marian-muenn/eib-drumcomputer/kicad/midi-interface/midi-interface-1.png

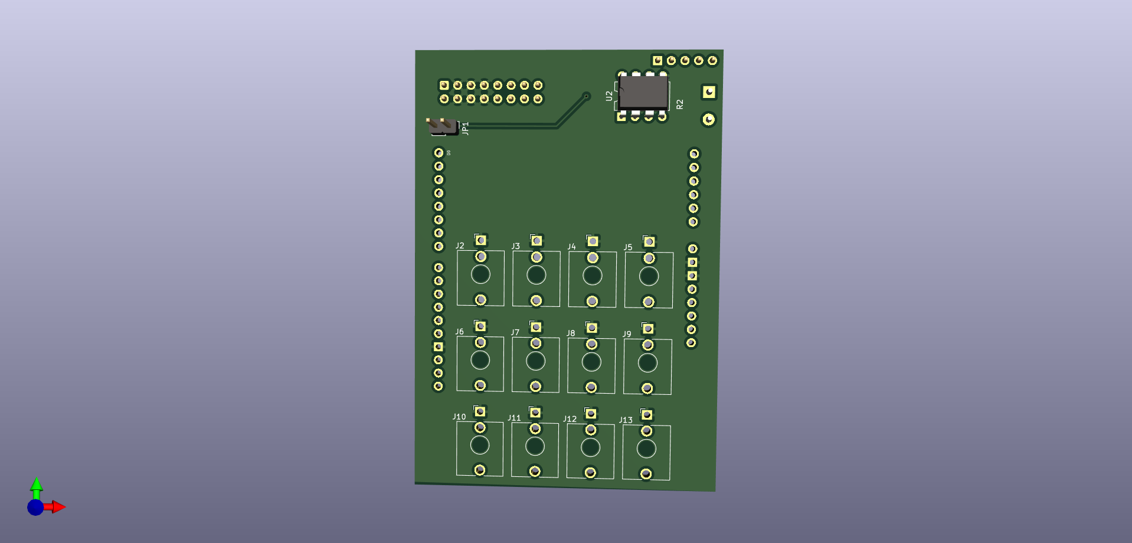
kicad/midi-interface/midi-interface-1.png
