marian-muenn/eib-drumcomputer/tex/montageanleitung/Images/doppel T filter.png

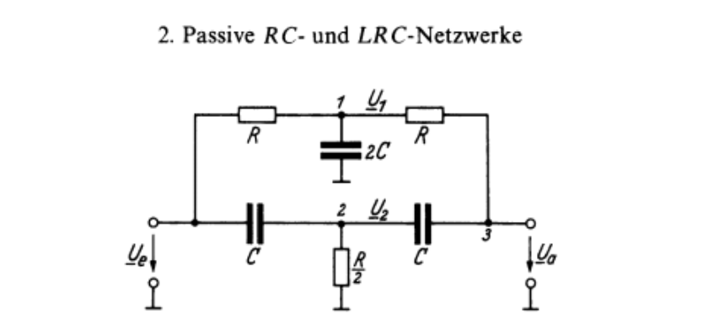
tex/montageanleitung/Images/doppel T filter.png
