marian-muenn/eib-drumcomputer/tex/montageanleitung/Images/Eurorack_Case_8253.jpg

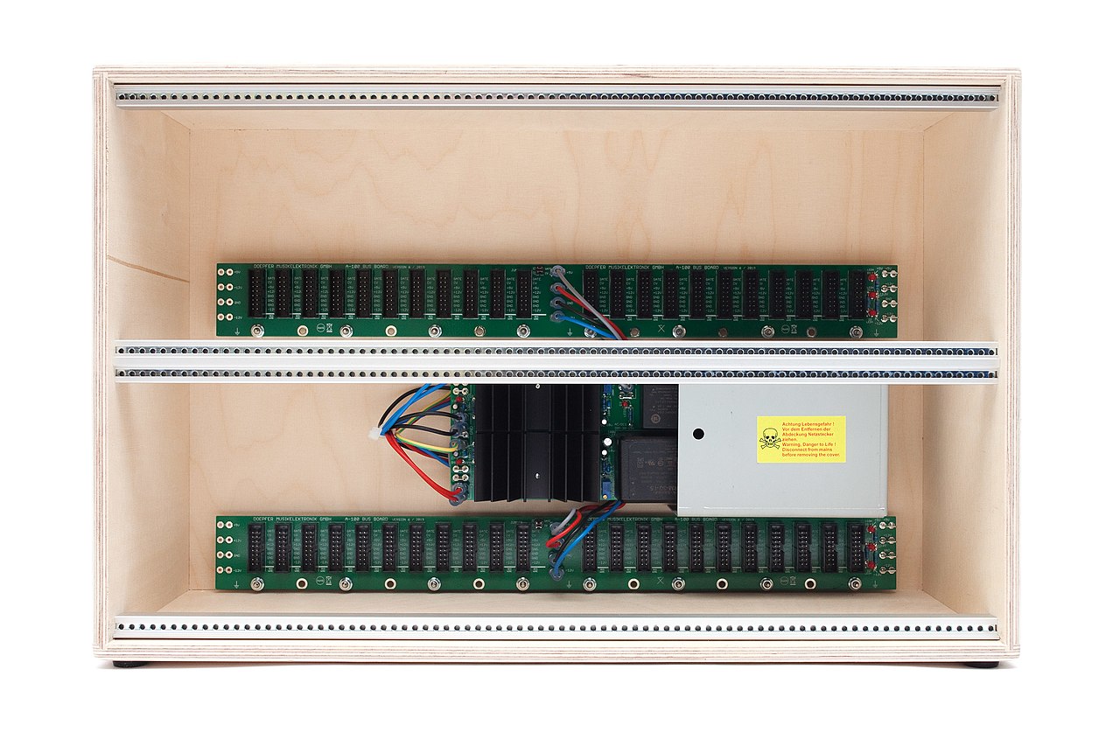
tex/montageanleitung/Images/Eurorack_Case_8253.jpg
