marian-muenn/eib-drumcomputer/tex/montageanleitung/Images/frequenzgang doppel t.png

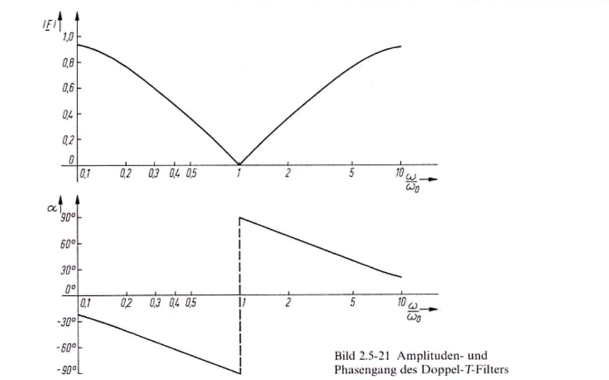
tex/montageanleitung/Images/frequenzgang doppel t.png
