marian-muenn/eib-drumcomputer/tex/montageanleitung/Images/image.png

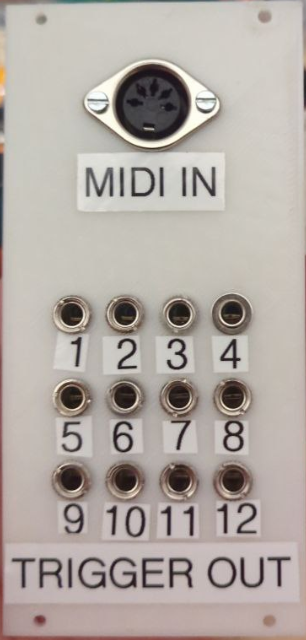
tex/montageanleitung/Images/image.png
