marian-muenn/eib-drumcomputer/tex/montageanleitung/Images/ltspice_bassdrum.jpg

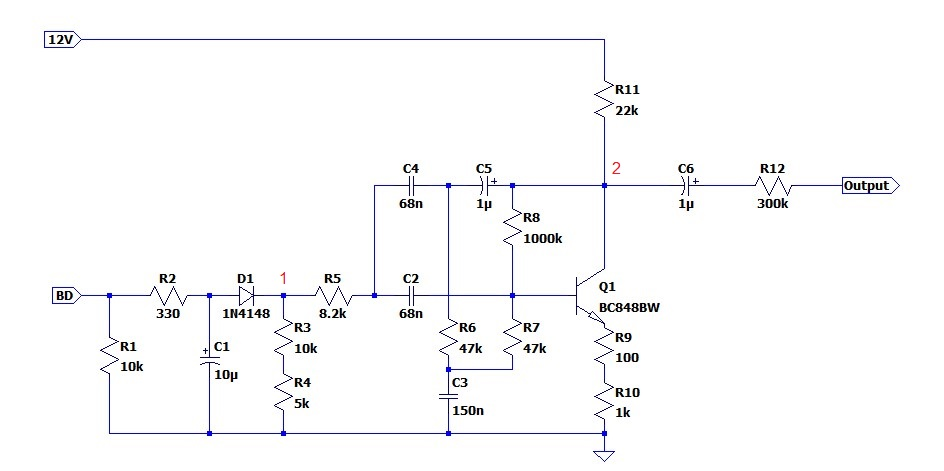
tex/montageanleitung/Images/ltspice_bassdrum.jpg
