marian-muenn/eib-drumcomputer/ltspice/Monostabiler Multivibrator/NE555.asc

C2: cap; 220n
C10: cap; 1µ
C11: cap; 10µ
C12: cap; 100n
Q3: npn
R18: res; 1k
R19: res; 47k
R20: res; 220
R21: res; 100
U1: NE555
V1: voltage; 12
V2: voltage; PULSE(0 5 0 1u 1u 50m 100m 4)
V3: voltage; 5
V4: voltage; -12
Named nets: +12V, 0, Trigger, +5V, output, -12V
.tran 250m
