marian-muenn/eib-drumcomputer/ltspice/bass_drum/bass_drum.asc

C3: polcap; 10µ; V=10
C4: cap; 68n
C5: cap; 68n
C6: cap; 150n
C7: polcap; 1µ; V=25
C8: polcap; 1µ; V=25
D1: diode; MURS120
Q1: npn; BC848BW
R1: res; 10k
R2: res; 10k
R5: res; 330
R7: res; 8.2k
R8: res; 10k
R9: res; 47k
R10: res; 47k
R11: res; 1000k
R12: res; 100
R13: res; 1k
R14: res; 22k
R15: res; 300k
V1: voltage; 12
V2: voltage; PULSE(0 5 10m 1u 1u 1m 2m 1); AC 1
Named nets: 12V, 0, BD, Output
.ac dec 250ms 1 20000
.wave bass_drum.wav 32 44100 output
