marian-muenn/eib-drumcomputer/ltspice/snare_drum_noise/snare_drum_noise.asc

B1: bv; V=30m*white(time*20000)
C1: cap; 56n
C2: cap; 8.2n
C3: cap; 1n
C5: cap; 1n
C6: cap; 3.3n
C9: cap; 10n
D1: diode; 1SS390SM
D2: diode; 1SS390SM
L1: ind; 100mH; Rser=82
L2: ind; 100mH; Rser=82
L3: ind; 100mH; Rser=82
Q1: npn; BC848BW
R1: res; 10k
R2: res; 1000k
R3: res; 470k
R4: res; 20k
R5: res; 560k
R18: res; 5000
V1: voltage; 12
V2: voltage; PULSE(0 5 10m 1u 1u 1m 2m 1); AC 1
Named nets: 12V, 0, trigger_snare, 12v, output, noise
.wave snare_drum_noise.wav 32 44100 output
.ac dec 150m 1 20000
