marian-muenn/eib-drumcomputer/ltspice/cymbal_1/cymbal_1.asc

B1: bv; V=20m*white(time*20000)
C1: cap; 180n
C2: cap; 47n
C3: cap; 1n
C5: cap; 4.7n
C6: cap; 6.8n
C9: cap; 10n
D1: diode; 1SS390SM
D2: diode; 1SS390SM
L2: ind; 33mH
Q1: npn; BC848BW
R1: res; 10k
R2: res; 1000k
R3: res; 470k
R4: res; 56k
R5: res; 390k
R18: res; 1500
V1: voltage; 12
V2: voltage; PULSE(0 5 10m 1u 1u 1m 2m 1)
Named nets: 12V, 0, trigger_snare, 12v, output, noise
.tran 250ms
.wave cymbal_1.wav 32 44100 output
