marian-muenn/eib-drumcomputer/ltspice/high_bongo/high_bongo.asc

C3: polcap; 10µ; V=10
C4: cap; 6.8n
C5: cap; 6.8n
C6: cap; 390n
C7: polcap; 1µ; V=25
C8: polcap; 0.47µ; V=25
D1: diode; DAN235E
Q1: npn; BC848BW
R1: res; 100k
R5: res; 330
R7: res; 8.2k
R8: res; 15k
R9: res; 27k
R10: res; 27k
R11: res; 1000k
R12: res; 100
R13: res; 1k
R14: res; 22k
R15: res; 560k
V1: voltage; 12
V2: voltage; PULSE(0 5 10m 1u 1u 1m 2m 1)
Named nets: 12V, 0, BD, Output
.tran 250ms
.wave high_bongo.wav 32 44100 output
