marian-muenn/eib-drumcomputer/ltspice/snare_drum_dry/snare_drum_dry.asc

C1: polcap; 1µ; V=25
C2: polcap; 470n; V=25
C3: polcap; 10µ; V=10
C4: cap; 22n
C5: cap; 22n
C6: cap; 56n
C7: polcap; 1µ; V=25
C8: polcap; 1µ; V=25
D1: diode; DAN235E
Q1: npn; BC848BW
Q2: npn; BC848BW
R1: res; 100k
R2: res; 39k
R3: res; 10k
R4: res; 560k
R5: res; 330
R6: res; 2.2k
R7: res; 8.2k
R8: res; 15k
R9: res; 27k
R10: res; 27k
R11: res; 1000k
R12: res; 100
R13: res; 1k
R14: res; 22k
R15: res; 680k
R16: res; 56k
R17: res; 2.2k
V1: voltage; 12
V2: voltage; PULSE(0 5 10m 1u 1u 1m 2m 1)
Named nets: 12V, 0, BD, output
.tran 250ms
.wave snare_drum_dry.wav 32 44100 output
