marian-muenn/eib-drumcomputer/kicad/line-out/line-out/line-out.kicad_sch

## KiCad design kicad/line-out/line-out/line-out.kicad_sch (2023-05-23)

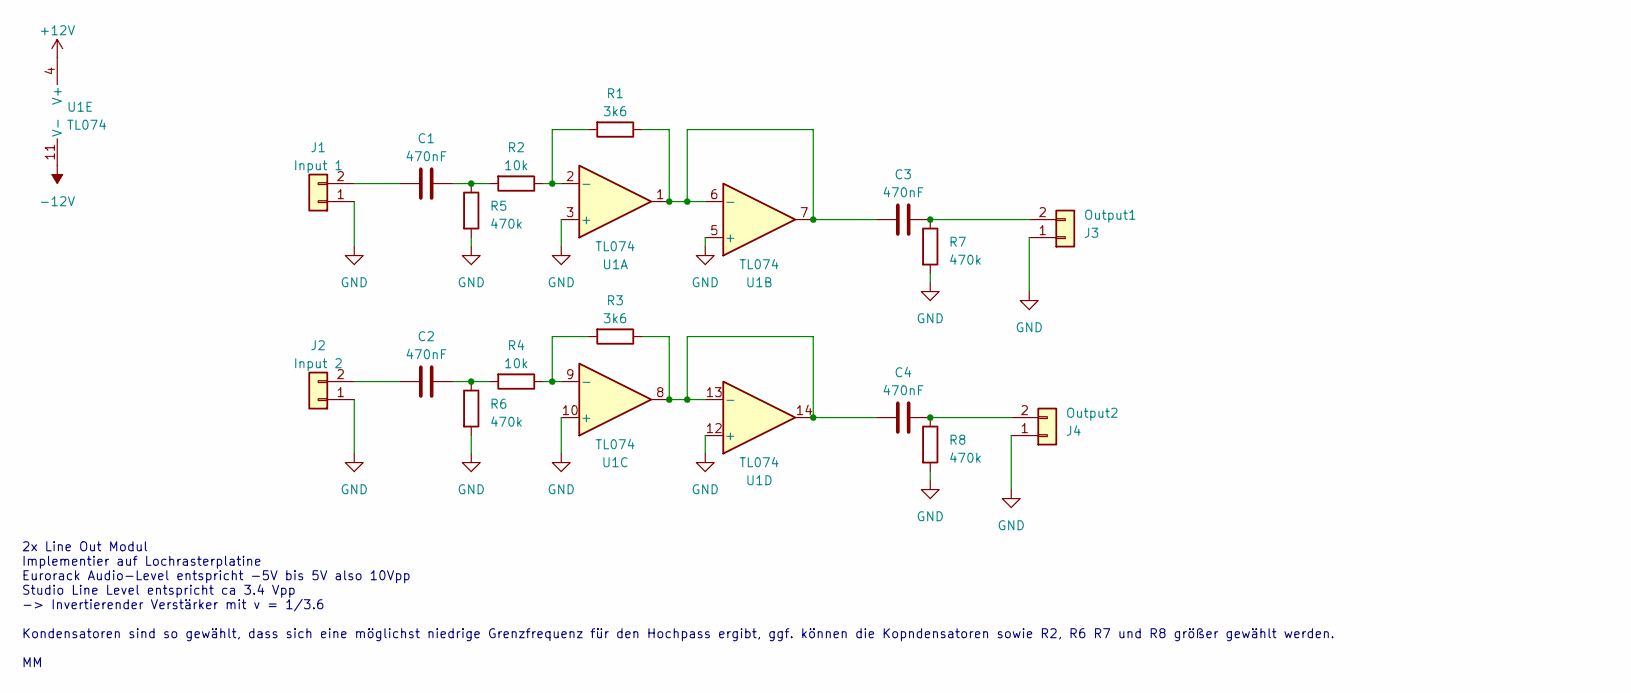
[picture p36: schematic line-out.kicad_sch]

Parts:
C1, C2, C3, C4: 470nF
J1: Input 1
J2: Input 2
J3: Output1
J4: Output2
R1, R3: 3k6
R2, R4: 10k
R5, R6, R7, R8: 470k
U1: TL074

Connections:
+12V: U1.4 (V+)
-12V: U1.11 (V-)
GND: J1.1, J2.1, J3.1, J4.1, R5.2, R6.2, R7.2, R8.2, U1.3 (+), U1.5 (+), U1.10 (+), U1.12 (+)
unnamed: C1.1, J1.2
unnamed: C1.2, R2.2, R5.1
unnamed: C2.1, J2.2
unnamed: C2.2, R4.2, R6.1
unnamed: C3.1, R1.1, U1.1, U1.6 (-), U1.7
unnamed: C3.2, J3.2, R7.1
unnamed: C4.1, R3.1, U1.8, U1.13 (-), U1.14
unnamed: C4.2, J4.2, R8.1
unnamed: R1.2, R2.1, U1.2 (-)
unnamed: R3.2, R4.1, U1.9 (-)

Notes on the sheet:
2x Line Out Modul Implementier auf Lochrasterplatine Eurorack Audio-Level entspricht -5V bis 5V also 10Vpp Studio Line Level entspricht ca 3.4 Vpp -> Invertierender Verstärker mit v = 1/3.6 Kondensatoren sind so gewählt, dass sich eine möglichst niedrige Grenzfrequenz für den Hochpass ergibt, ggf. 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
